LiftLaboratory/Alpha/Rack_Support_Mockup_Top v4.stl

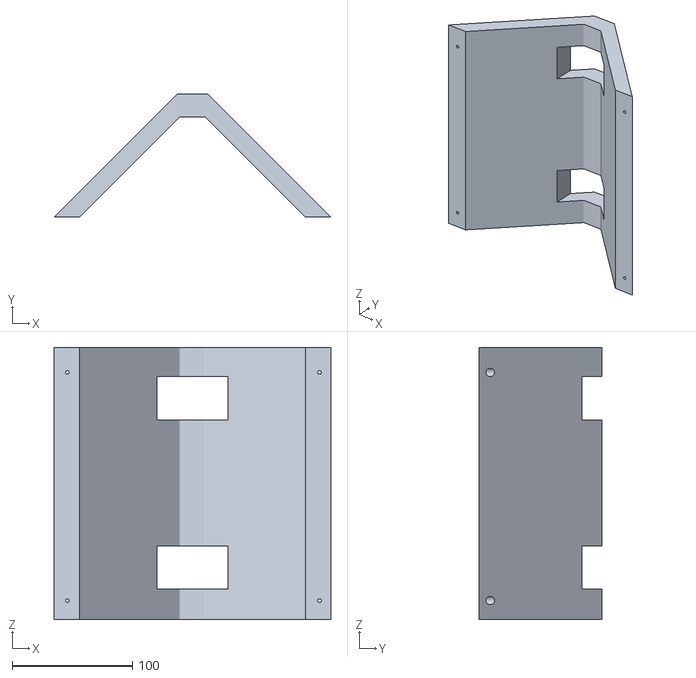
[picture p21: CAD file, 2022-12-01]
Rack_Support_Mockup_Top v4.stl
230.8 x 102.9 x 227.0
