LiftLaboratory/Alpha/Top Wing Attachment v23.stl

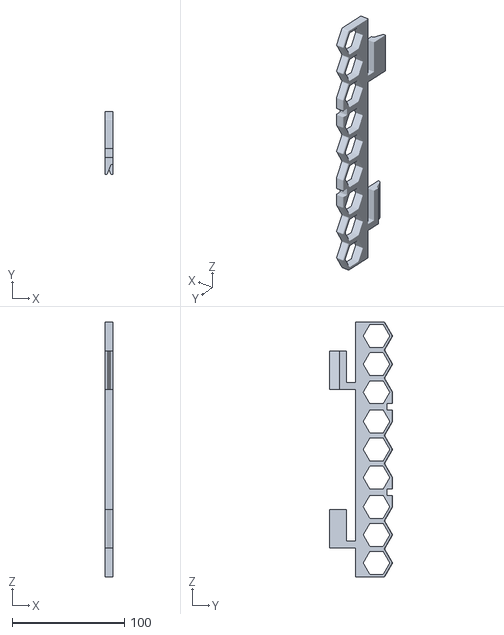
[picture p22: CAD file, 2022-12-01]
Top Wing Attachment v23.stl
7.50 x 56.5 x 227.0
