LiftLaboratory/Alpha/Charger_Holster_v7.stl

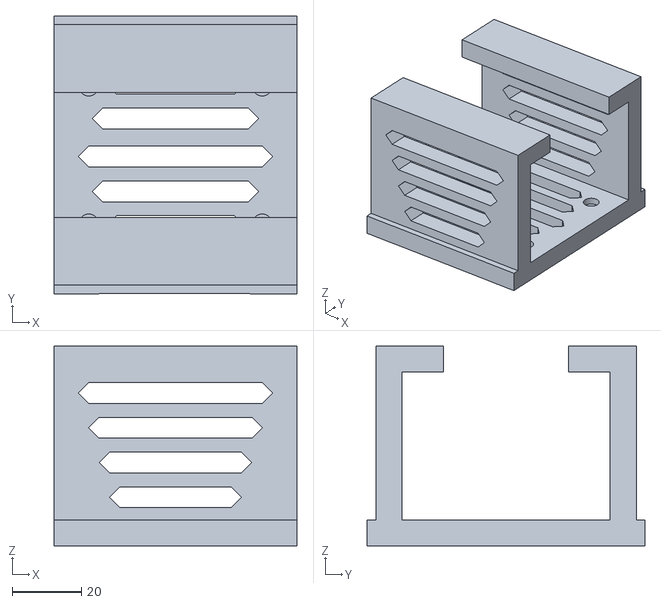
[picture p23: CAD file, 2022-12-01]
Charger_Holster_v7.stl
70.0 x 80.0 x 57.5
