LiftLaboratory/Alpha/IncubatorPlatform_Alone v11.stl

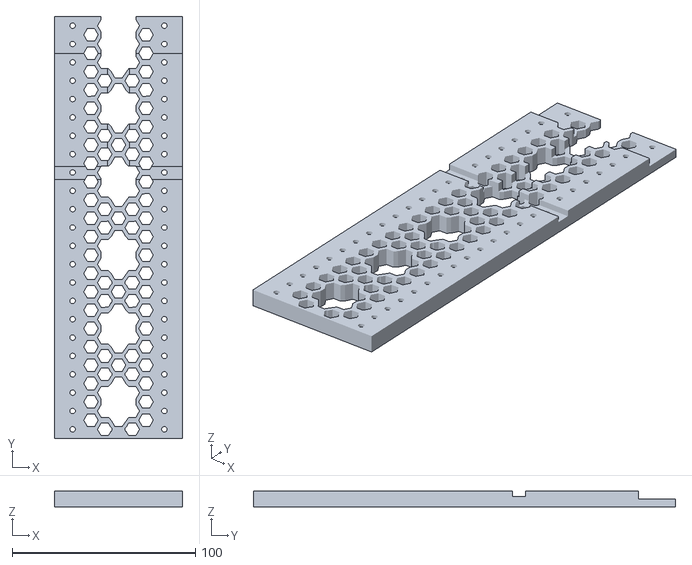
[picture p24: CAD file, 2022-12-01]
IncubatorPlatform_Alone v11.stl
70.0 x 230.0 x 8.50
