LiftLaboratory/Alpha/Rack_Support_Mockup_Botttom v5.stl

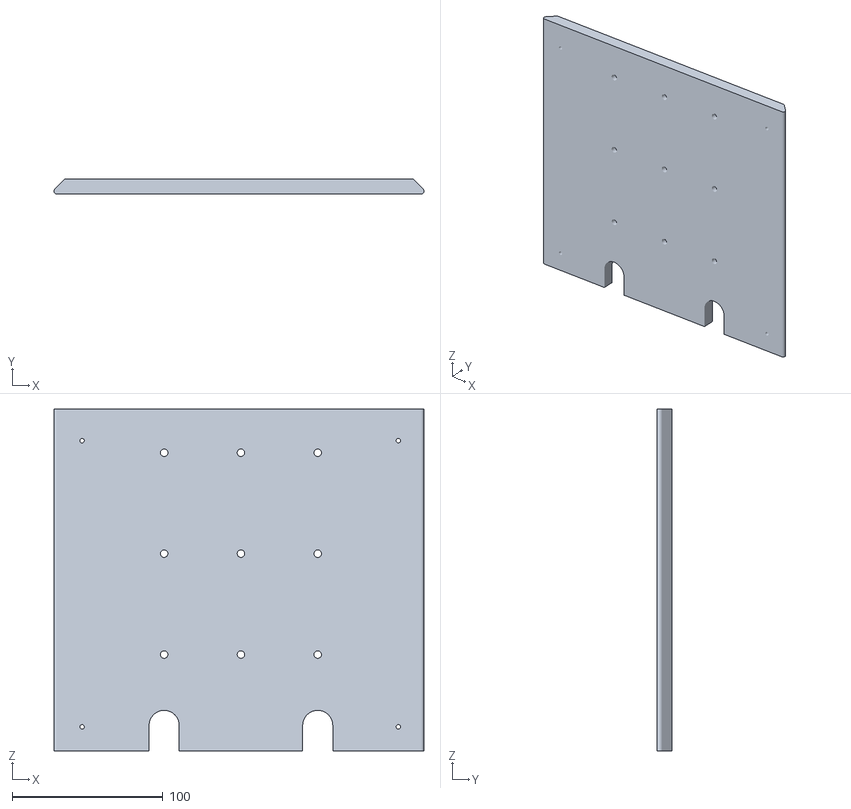
[picture p25: CAD file, 2022-12-01]
Rack_Support_Mockup_Botttom v5.stl
245.6 x 10.2 x 227.0
