LiftLaboratory/Alpha/Bottom Wing Attachment v8.stl

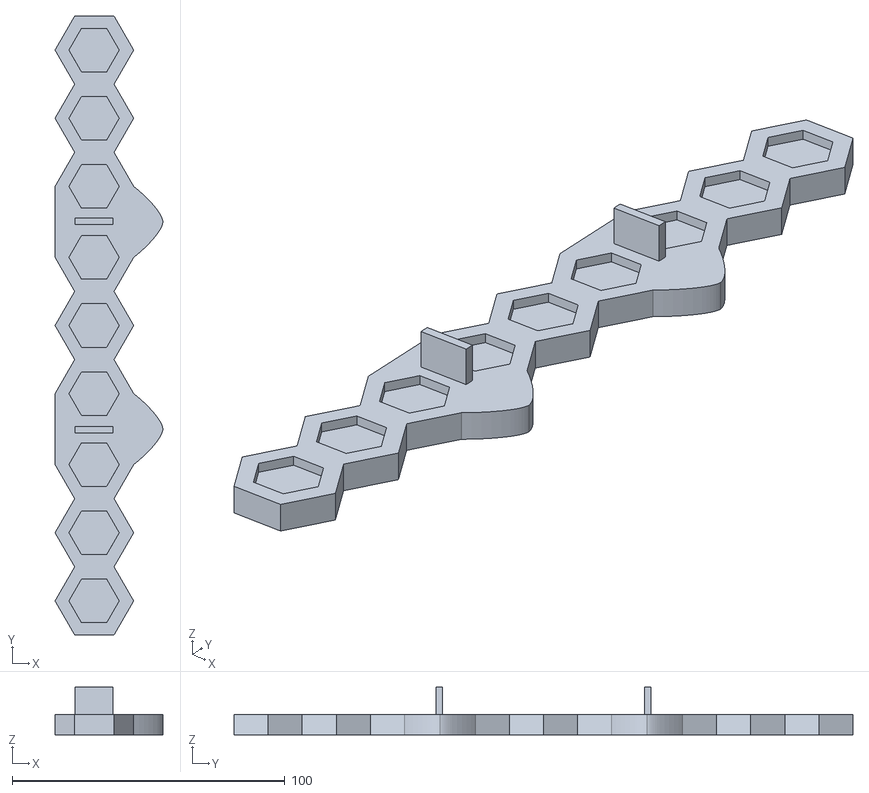
[picture p26: CAD file, 2022-12-01]
Bottom Wing Attachment v8.stl
39.6 x 227.0 x 17.5
