LiftLaboratory/Alpha/HingePieceShort_v5.stl

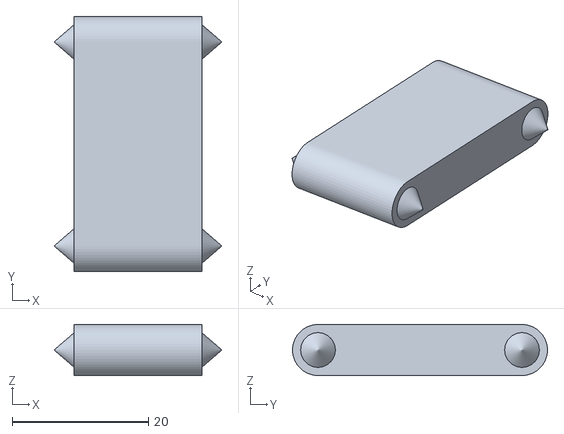
[picture p27: CAD file, 2022-10-27]
HingePieceShort_v5.stl
24.7 x 37.5 x 7.50
