LiftLaboratory/Alpha/HingePieceLong_v12.stl

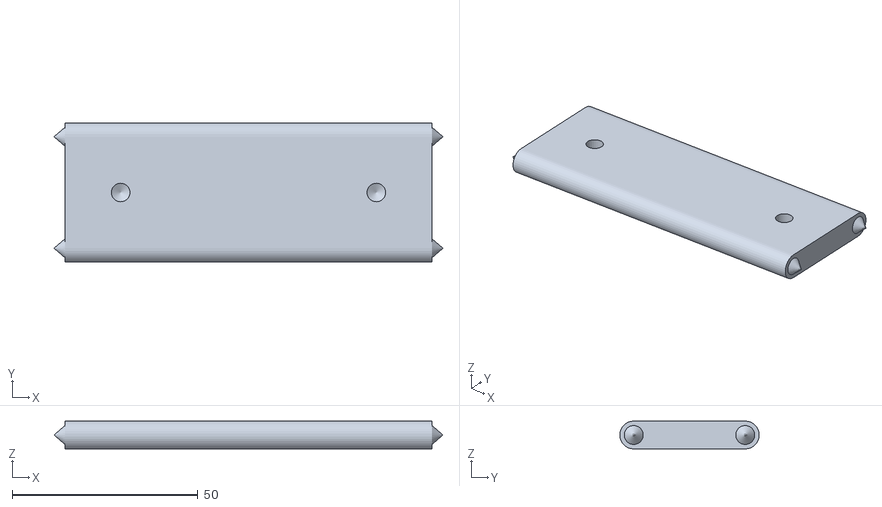
[picture p28: CAD file, 2022-10-27]
HingePieceLong_v12.stl
104.7 x 37.5 x 7.50
